Vithushikan38/PATIENT-MONITORING-IN-AMBULANCE-AND-OTHER-VEHICLES/ArduinoCodes/Components/NEO6M.ino

#include <TinyGPS++.h>

// Use HardwareSerial on ESP32 (Serial2 is available for external devices)
HardwareSerial gpsSerial(2);  // UART2 (Can use different pins)

// Define GPS RX & TX Pins
#define RXPin 16  // Connect this to GPS TX
#define TXPin 17  // Connect this to GPS RX
#define GPSBaud 9600

TinyGPSPlus gps;

void displayInfo()
{
  if (gps.location.isValid())
  {
    Serial.print("Latitude: ");
    Serial.println(gps.location.lat(), 6);
    Serial.print("Longitude: ");
    Serial.println(gps.location.lng(), 6);
    Serial.print("Altitude: ");
    Serial.println(gps.altitude.meters());
  }
  else
  {
    Serial.println("Location: Not Available");
  }
  
  Serial.print("Date: ");
  if (gps.date.isValid())
  {
    Serial.print(gps.date.month());
    Serial.print("/");
    Serial.print(gps.date.day());
    Serial.print("/");
    Serial.println(gps.date.year());
  }
  else
  {
    Serial.println("Not Available");
  }

  Serial.print("Time: ");
  if (gps.time.isValid())
  {
    if (gps.time.hour() < 10) Serial.print(F("0"));
    Serial.print(gps.time.hour());
    Serial.print(":");
    if (gps.time.minute() < 10) Serial.print(F("0"));
    Serial.print(gps.time.minute());
    Serial.print(":");
    if (gps.time.second() < 10) Serial.print(F("0"));
    Serial.print(gps.time.second());
    Serial.print(".");

    if (gps.time.centisecond() < 10) Serial.print(F("0"));
    Serial.println(gps.time.centisecond());
  }
  else
  {
    Serial.println("Not Available");
  }

  Serial.println();
  Serial.println();
  delay(1000);
}

void setup()
{
  Serial.begin(115200);  // Use higher baud rate for ESP32
  gpsSerial.begin(GPSBaud, SERIAL_8N1, RXPin, TXPin);  // Set pins for ESP32
}

void loop()
{
  while (gpsSerial.available() > 0)
    if (gps.encode(gpsSerial.read()))
      displayInfo();

  if (millis() > 5000 && gps.charsProcessed() < 10)
  {
    Serial.println("No GPS detected");
    while (true);
  }
}
